kabies-sickkk/ROBOT-Jetbot-ESP32-Control-/Baocao/T8_Do_An_IOT_DHL_doc.docx

| BỘ GIÁO DỤC VÀ ĐÀO TẠO TRƯỜNG ĐẠI HỌC CÔNG NGHỆ TP. HỒ CHÍ MINH

ĐỒ ÁN MÔN HỌC

ĐỒ ÁN IOT

HỆ THỐNG XE THÔNG MINH ĐIỀU KHIỂN

KHÔNG DÂY ỨNG DỤNG IOT

Ngành: Robot và trí tuệ nhân tạo

Lớp: 22DRTA1

Giảng viên hướng dẫn : Ths. NGÔ AN THUYÊN

Sinh viên thực hiện: | MSSV: | Lớp:
Nguyễn Văn Đạt | 2286300010 | 22DRTA1
Huỳnh Long | 2286300028 | 22DRTA1
Nguyễn Chấn Huy | 2286300020 | 22DRTA1

Tp.HCM, ngày … tháng … năm

| BỘ GIÁO DỤC VÀ ĐÀO TẠO TRƯỜNG ĐẠI HỌC CÔNG NGHỆ TP. HỒ CHÍ MINH

ĐỒ ÁN MÔN HỌC

ĐỒ ÁN IOT

HỆ THỐNG XE THÔNG MINH ĐIỀU KHIỂN

KHÔNG DÂY ỨNG DỤNG IOT

Ngành: Robot và trí tuệ nhân tạo

Lớp: 22DRTA1

Giảng viên hướng dẫn : Ths. NGÔ AN THUYÊN

Sinh viên thực hiện: | MSSV: | Lớp:
Nguyễn Văn Đạt | 2286300010 | 22DRTA1
Huỳnh Long | 2286300028 | 22DRTA1
Nguyễn Chấn Huy | 2286300020 | 22DRTA1

Tp.HCM, ngày … tháng … năm

VIỆN KỸ THUẬT HUTECH

PHIẾU GIAO ĐỀ TÀI

TÊN MÔN HỌC : Đồ án IOT

NGÀNH: Robot và Trí tuệ nhân tạo

1. Họ và tên sinh viên/ nhóm sinh viên được giao đề tài (sĩ số trong nhóm: 03):

(1) Nguyễn Văn Đạt MSSV: 2286300010…… Lớp: 22DRTA1

(2) Huỳnh Long MSSV: 2286300028…… Lớp: 22DRTA1

(3) Nguyễn Chấn Huy MSSV: 2286300020…… Lớp: 22DRTA1

2. Tên đề tài: Hệ thống xe thông minh điều khiển không dây ứng dụng IoT
3. Các dữ liệu ban đầu:

- Kiến thức nền tảng về IoT, hệ thống điều khiển nhúng, và kết nối không dây.

- Các linh kiện phần cứng: vi điều khiển (ESP32/Arduino), cảm biến khoảng cách/IR/siêu âm, động cơ, pin, mạch điều khiển động cơ.

- Phần mềm: Dashboard/Webserver (trên máy tính hoặc điện thoại), công cụ lập trình (Arduino IDE, Python, hoặc tương đương).

- Tài liệu tham khảo từ các nghiên cứu trước về xe thông minh và ứng dụng IoT.

4. Nội dung nhiệm vụ :

- Nghiên cứu, thiết kế và chế tạo mô hình xe thông minh có khả năng điều khiển từ xa qua IoT.

- Tích hợp hệ thống cảm biến để thu thập dữ liệu (tốc độ, hướng di chuyển, mức pin, khoảng cách vật cản).

- Xây dựng giao diện Dashboard/Webserver để giám sát và điều khiển xe theo thời gian thực.

- Thiết kế PCB riêng cho khối điều khiển động cơ và khối cảm biến.

- Ứng dụng IoT để kết nối xe với server, lưu trữ dữ liệu hành trình và có thể mở rộng giám sát qua cloud.

- Nâng cao (tùy điều kiện):

- Tích hợp AI để xe nhận diện line đường hoặc vật cản.
- Tích hợp camera để quan sát trực tiếp từ xa.
5. Kết quả tối thiểu phải có:

1) Xe thông minh có thể điều khiển từ xa qua IoT (dashboard/Webserver).

2) Hệ thống giám sát thời gian thực trạng thái xe (tốc độ, hướng, mức pin, dữ liệu cảm biến).

3) Báo cáo đầy đủ: mô tả, thiết kế, thực nghiệm, kết quả đạt được, tài liệu tham khảo.

Ngày giao đề tài: ……./……../……… Ngày nộp báo cáo: ……./……../………

Sinh viên thực hiện (Ký và ghi rõ họ tên các thành viên) Nguyễn Văn Đạt Huỳnh Long Nguyễn Chấn Huy | TP. HCM, ngày … tháng … năm ………. Giảng viên hướng dẫn (Ký và ghi rõ họ tên) Ngô An Thuyên

Kế hoạch kiểm thử và đánh giá hệ thống (áp dụng cho xe IoT ESP32 – HiveMQ – Node-RED)

1) Lập kế hoạch kiểm thử

Kế hoạch kiểm thử được xây dựng dựa trên các chức năng cốt lõi của hệ thống gồm: kết nối IoT, điều khiển xe, giám sát dữ liệu encoder, và stream ESP32-CAM. Nhóm chia kiểm thử theo từng mô-đun (unit test theo khối) và kiểm thử tích hợp (integration test toàn hệ thống) nhằm khoanh vùng lỗi nhanh và đảm bảo tính ổn định khi vận hành thực tế. Mỗi chức năng được gắn với các điều kiện kiểm tra cụ thể như: môi trường WiFi ổn định/không ổn định, khoảng cách điều khiển khác nhau, xe chạy không tải/có tải nhẹ, bật/tắt stream encoder, bật/tắt camera và kiểm tra độ trễ hiển thị trên Dashboard.

Danh sách chức năng cần kiểm tra bao gồm: (i) ESP32 kết nối WiFi, tự reconnect khi mất mạng; (ii) ESP32 kết nối MQTT (HiveMQ), subscribe/publish đúng topic; (iii) Node-RED gửi lệnh điều khiển và xe phản hồi đúng hành vi (tiến/lùi/rẽ/dừng); (iv) encoder đếm xung chính xác, tính RPM hợp lý và hiển thị line chart; (v) cơ chế bật/tắt stream encoder hoạt động đúng (chỉ gửi khi bật); (vi) ESP32-CAM stream hiển thị trên Dashboard, kiểm tra độ ổn định khi chạy lâu; và (vii) kiểm thử an toàn: khi mất kết nối, hệ thống có cảnh báo trạng thái (online/offline) và hạn chế hành vi ngoài ý muốn.

2) Ghi lại kết quả thực tế

Trong quá trình kiểm thử, nhóm ghi nhận kết quả bằng các dạng minh chứng gồm dữ liệu đo, ảnh chụp màn hình và video vận hành. Đối với dữ liệu đo, nhóm theo dõi các bản tin MQTT nhận được trên HiveMQ/Node-RED (topic encoder và topic trạng thái), kiểm tra payload có đúng định dạng và tần suất gửi có đúng theo thiết kế. Trên Dashboard, nhóm ghi lại các thông số hiển thị như trạng thái xe, trạng thái kết nối, và đồ thị RPM theo thời gian. Việc ghi nhận liên tục trong nhiều phiên chạy giúp đánh giá được tính ổn định và phát hiện các tình huống bất thường (dao động lớn, mất dữ liệu, trễ hiển thị).

Về minh chứng trực quan, nhóm chụp ảnh Dashboard ở các trạng thái quan trọng: (i) xe đang nhận lệnh điều khiển; (ii) biểu đồ RPM có dữ liệu đang thay đổi; (iii) trạng thái online/offline; và (iv) giao diện hiển thị stream ESP32-CAM. Ngoài ra, nhóm quay video ngắn thể hiện quy trình vận hành đầy đủ: bấm nút điều khiển trên Dashboard → xe chuyển động → RPM thay đổi trên chart → camera stream hiển thị đồng thời. Các minh chứng này được dùng để đối chiếu với mục tiêu ban đầu và làm cơ sở đánh giá kết quả đạt được trong báo cáo.

3) Phát hiện và xử lý lỗi

Trong quá trình thử nghiệm, nhóm ghi nhận một số lỗi phổ biến phát sinh do đặc thù hệ thống nhúng và môi trường IoT. Các lỗi điển hình gồm: mất kết nối MQTT/WiFi, độ trễ điều khiển khi mạng yếu, dữ liệu encoder nhiễu hoặc nhảy bất thường, và camera không khởi tạo/stream không ổn định khi nguồn cấp không đủ dòng. Nguyên nhân thường liên quan đến chất lượng WiFi, cấu hình broker, dây nguồn/động cơ gây sụt áp, và nhiễu điện từ sinh ra khi động cơ hoạt động. Việc khoanh vùng nguyên nhân được thực hiện theo nguyên tắc: kiểm tra theo tầng (nguồn → phần cứng → kết nối → phần mềm → dashboard), đồng thời đối chiếu log Serial và log Node-RED để xác định lỗi nằm ở phía thiết bị hay phía server/giao diện.

Các phương án khắc phục được áp dụng theo từng nhóm lỗi: với lỗi kết nối, hệ thống được bổ sung/duy trì cơ chế reconnect và kiểm tra trạng thái định kỳ; với dữ liệu encoder nhiễu, nhóm tối ưu cách đọc xung (đi dây tín hiệu gọn, tách khỏi dây động cơ, dùng pull-up phù hợp) và có thể bổ sung lọc dữ liệu nhẹ khi hiển thị; với lỗi camera, nhóm ưu tiên đảm bảo nguồn cấp ổn định và giảm cấu hình hình ảnh khi băng thông hạn chế. Sau khi sửa, nhóm thực hiện kiểm thử lại theo đúng kịch bản ban đầu để xác nhận lỗi đã được xử lý và hệ thống đạt độ ổn định mong muốn.

4) Điều chỉnh hệ thống sau khi tối ưu

Dựa trên kết quả kiểm thử và các lỗi ghi nhận, nhóm tiến hành điều chỉnh hệ thống theo hướng tăng độ ổn định và cải thiện trải nghiệm điều khiển. Về tham số phần mềm, nhóm điều chỉnh chu kỳ gửi dữ liệu encoder (tần suất publish) để cân bằng giữa độ mượt hiển thị và tải truyền thông, đồng thời áp dụng cơ chế bật/tắt stream để tránh gửi dữ liệu không cần thiết. Về thuật toán, nhóm tối ưu cách cập nhật tốc độ theo chu kỳ cố định để dữ liệu RPM ổn định hơn và dễ quan sát trên biểu đồ. Trên Dashboard, nhóm có thể tổ chức lại bố cục giao diện, tăng tính trực quan của trạng thái kết nối và cảnh báo để người dùng nhận biết nhanh khi có sự cố.

Về phần cứng, các điều chỉnh tập trung vào nguồn và đi dây nhằm giảm nhiễu và sụt áp: tách nguồn động cơ và nguồn điều khiển hợp lý, bổ sung tụ lọc tại điểm cấp nguồn, rút ngắn dây công suất và cố định dây tín hiệu encoder. Các cải tiến này giúp hệ thống vận hành ổn định hơn khi xe tăng tốc hoặc đổi hướng, giảm tình trạng reset thiết bị và cải thiện độ tin cậy của dữ liệu giám sát. Tổng hợp các điều chỉnh sau tối ưu được ghi rõ trong báo cáo như một minh chứng cho quá trình hoàn thiện và nâng cao chất lượng hệ thống.

BM01/ĐAMH/VKT Đề số:…….
