kabies-sickkk/ROBOT-Jetbot-ESP32-Control-/Picture/Picture IoT/pcb b.png

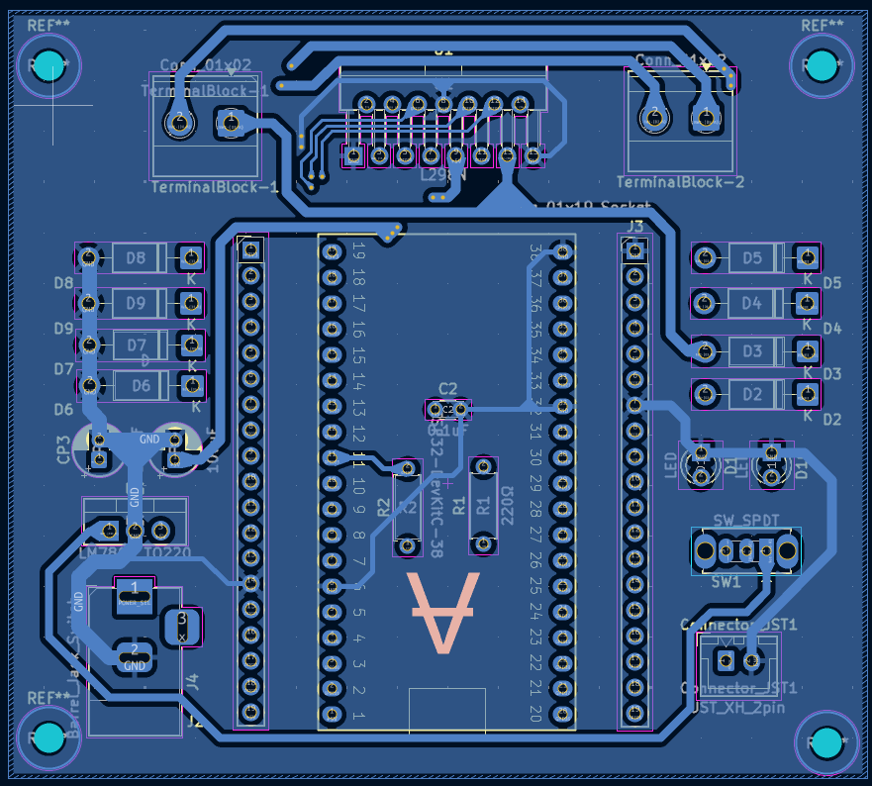
Picture/Picture IoT/pcb b.png
