kabies-sickkk/ROBOT-Jetbot-ESP32-Control-/Picture/Picture IoT/z7338781888690_a56b1c9e72bbe3088352e7ef60286838.jpg

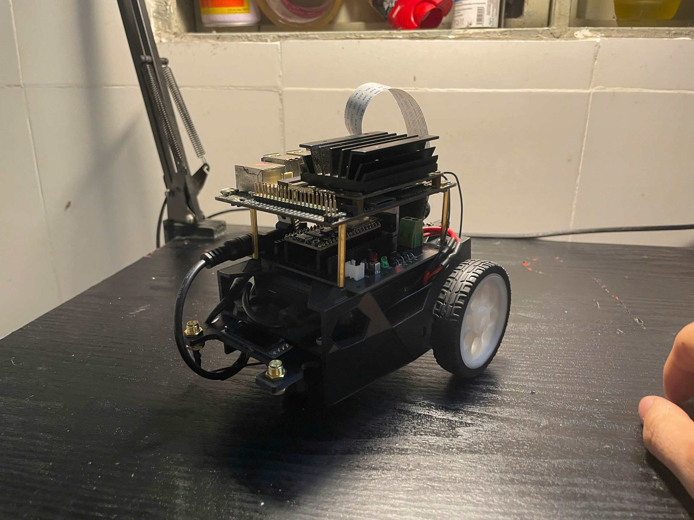
Picture/Picture IoT/z7338781888690_a56b1c9e72bbe3088352e7ef60286838.jpg
