kabies-sickkk/ROBOT-Jetbot-ESP32-Control-/Picture/Picture IoT/z7338781902327_4d1b3d4b1b1a15546500e21a4426a787.jpg

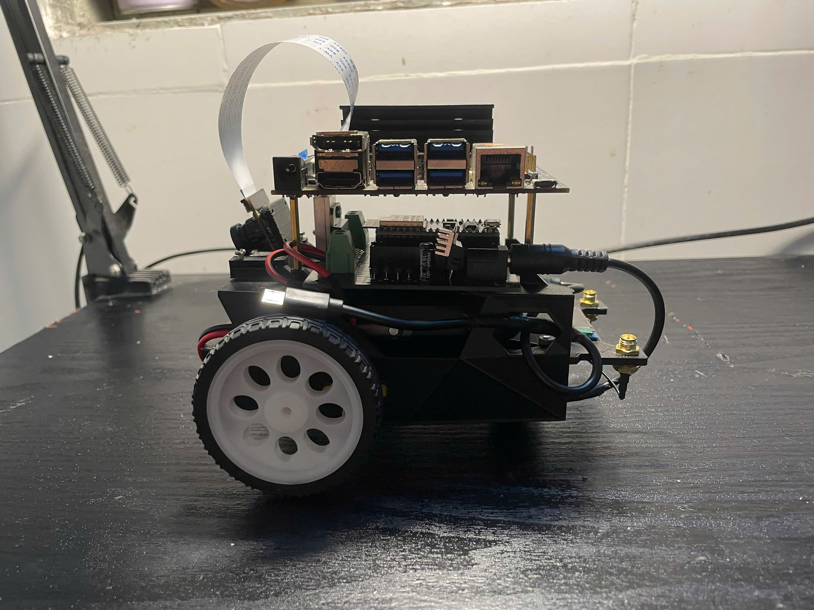
Picture/Picture IoT/z7338781902327_4d1b3d4b1b1a15546500e21a4426a787.jpg
